antmicro/pdm-microphone-board/assets/previews/layer1.png

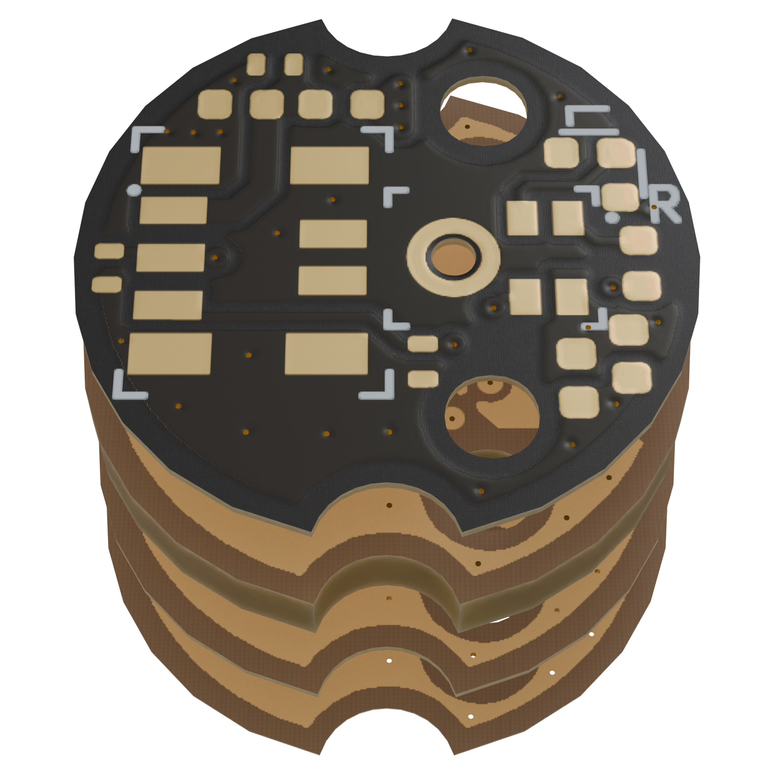
assets/previews/layer1.png
