antmicro/pdm-microphone-board/assets/previews/layer2.png

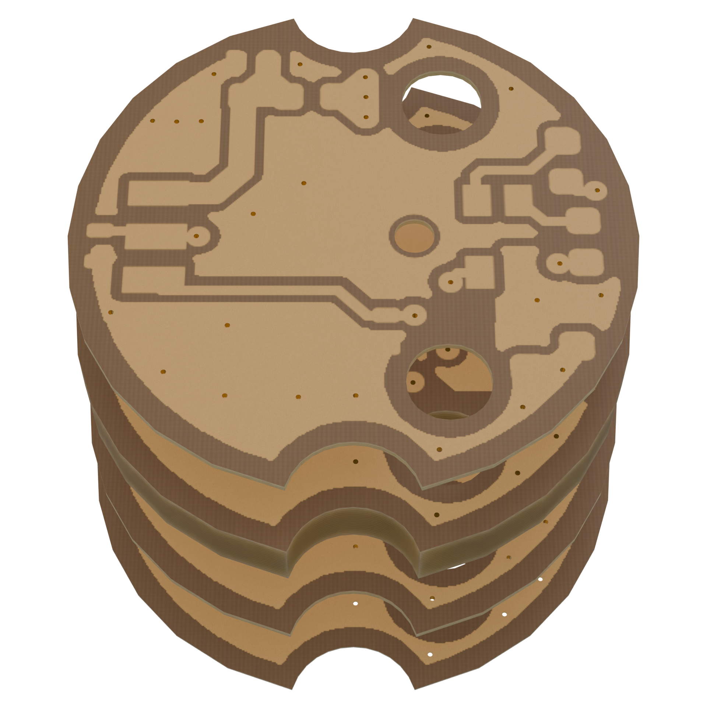
assets/previews/layer2.png
