antmicro/pdm-microphone-board/assets/previews/layer3.png

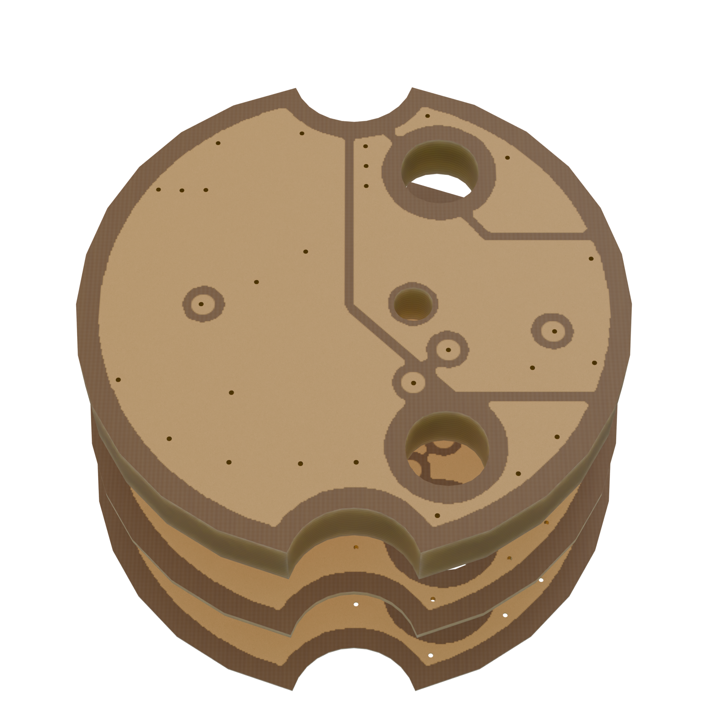
assets/previews/layer3.png
