antmicro/pdm-microphone-board/assets/previews/layer4.png

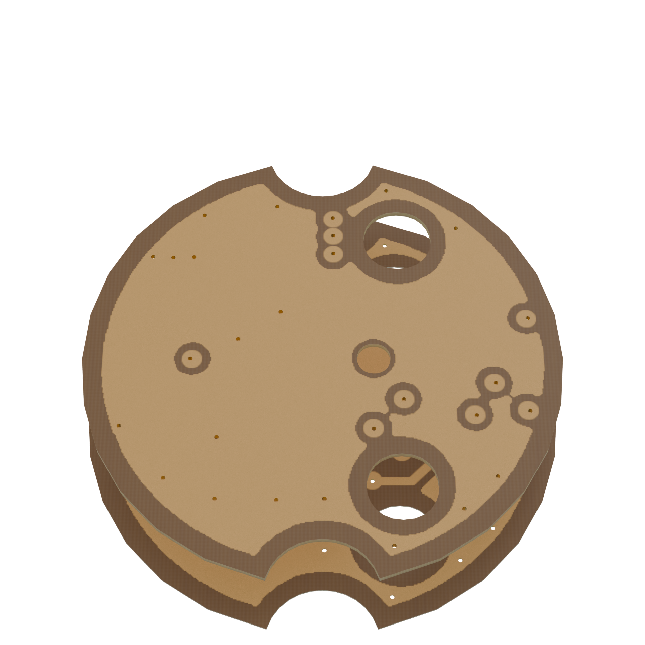
assets/previews/layer4.png
