antmicro/pdm-microphone-board/assets/previews/layer5.png

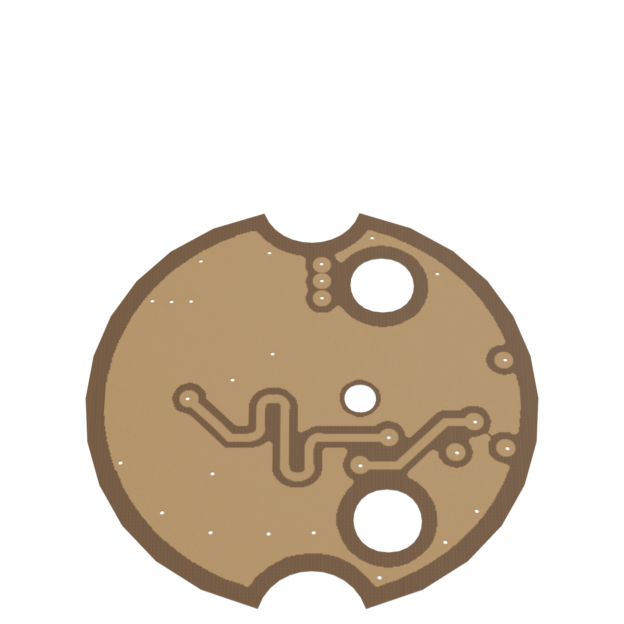
assets/previews/layer5.png
