antmicro/pdm-microphone-board/assets/previews/leftB.png

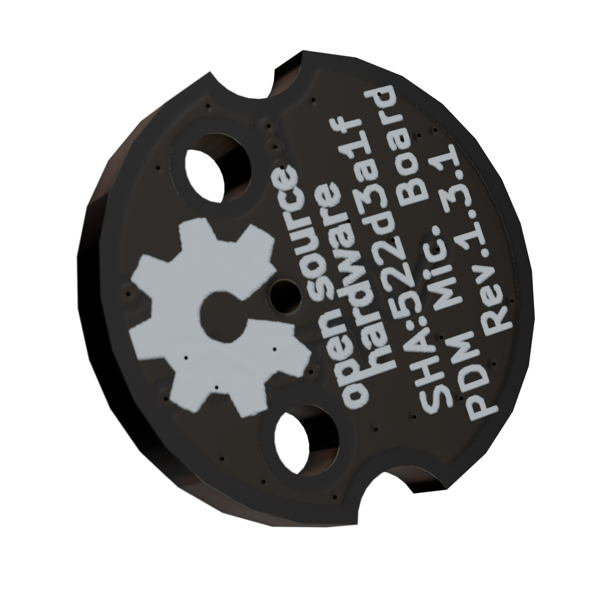
assets/previews/leftB.png
