antmicro/pdm-microphone-board/assets/previews/leftT.png

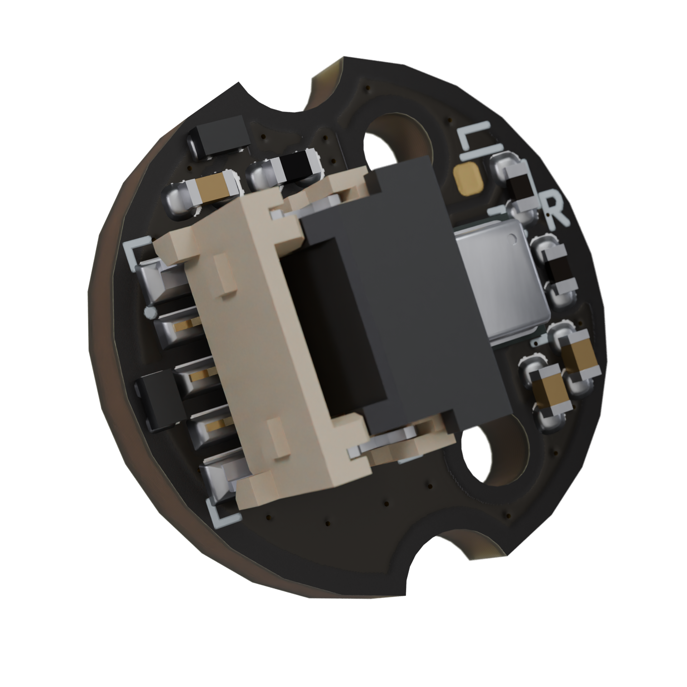
assets/previews/leftT.png
