antmicro/pdm-microphone-board/assets/previews/orthoB.png

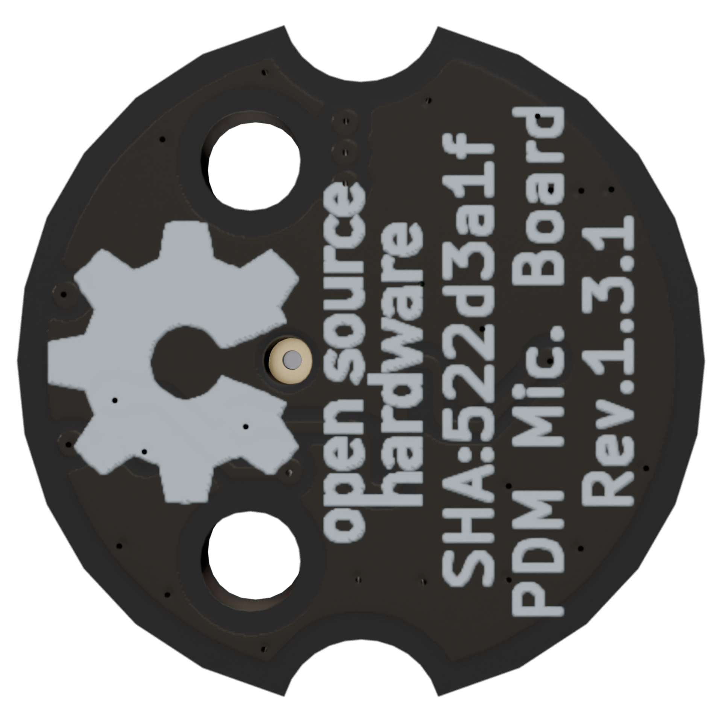
assets/previews/orthoB.png
