antmicro/pdm-microphone-board/assets/previews/rightB.png

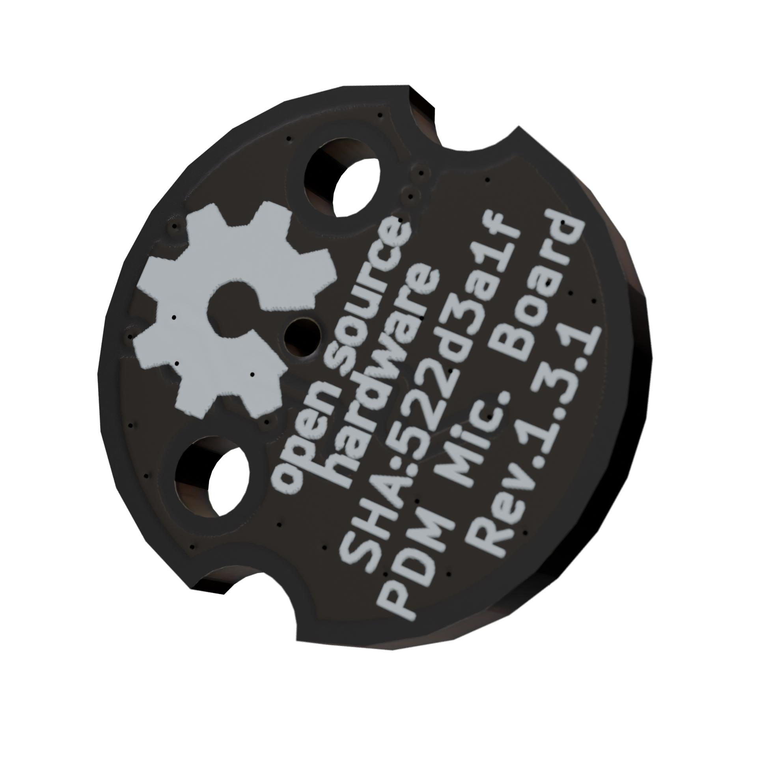
assets/previews/rightB.png
