antmicro/pdm-microphone-board/assets/previews/rightT.png

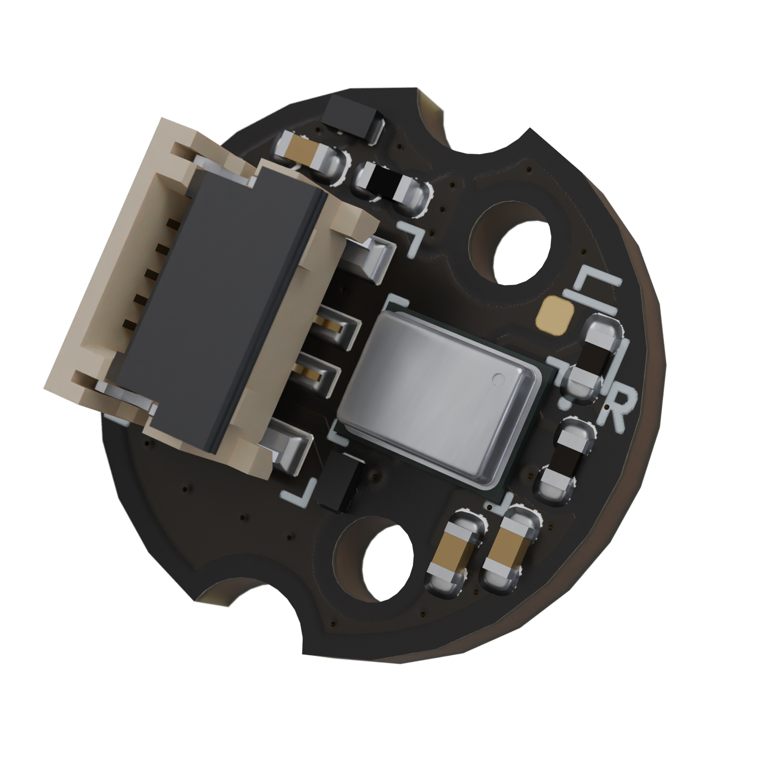
assets/previews/rightT.png
