antmicro/pdm-microphone-board/assets/wireframe/wireframe_wireframe_descriptions_bottom.png

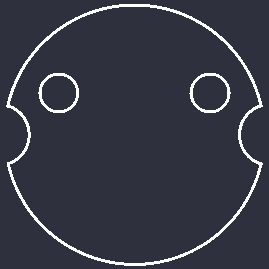
assets/wireframe/wireframe_wireframe_descriptions_bottom.png
