antmicro/pdm-microphone-board/assets/wireframe/wireframe_wireframe_dimensions.png

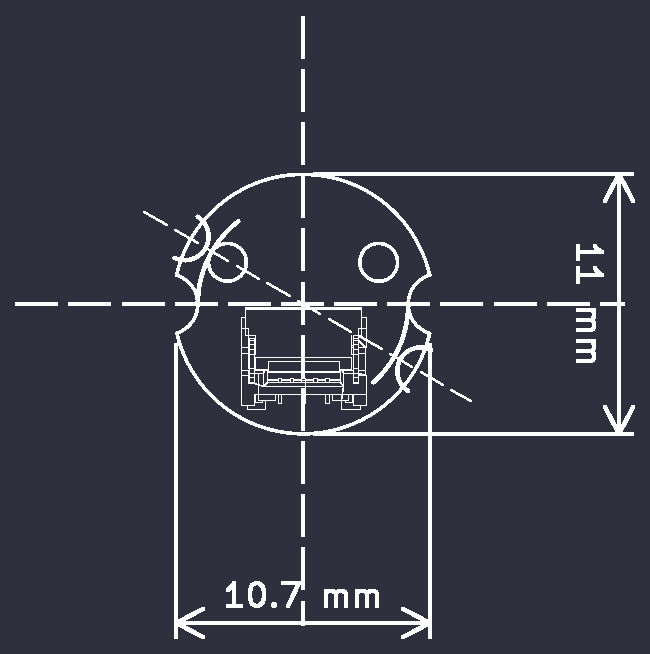
assets/wireframe/wireframe_wireframe_dimensions.png
