antmicro/pdm-microphone-board/assets/wireframe/wireframe_wireframe_dimensions_bottom.png

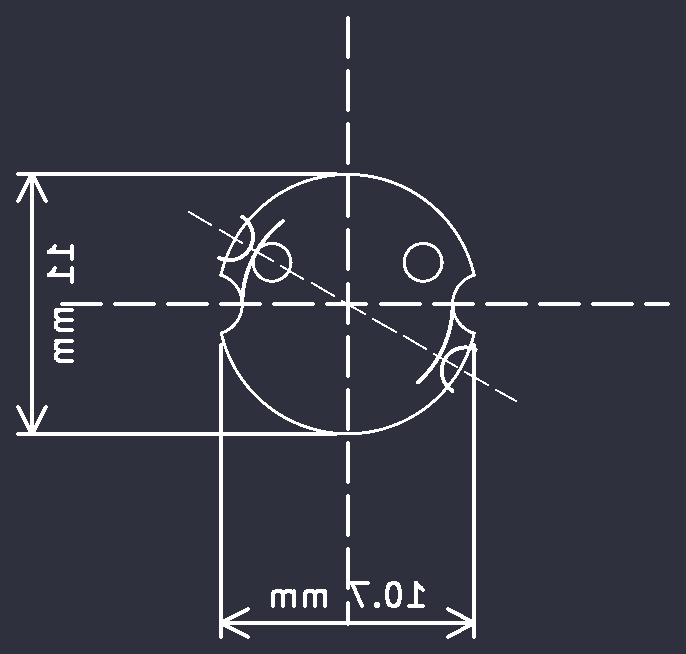
assets/wireframe/wireframe_wireframe_dimensions_bottom.png
